sjgray/pet-cbm-rom-adapters/multi-edit-rom/MultiEditROM.jpg

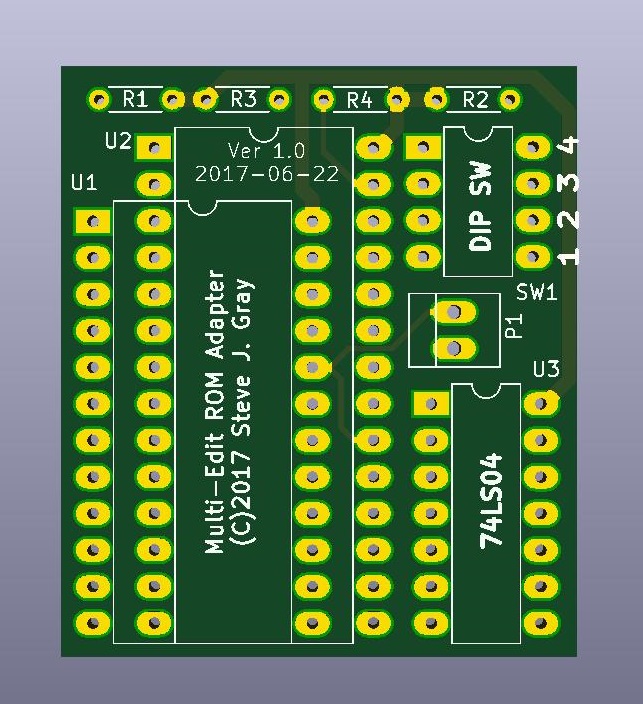
multi-edit-rom/MultiEditROM.jpg
